Lastrellik/Calico-Home-Security/src/Properties.h

/*
  Properties.h - A class for Properties

  This class is intended to be included in any class which needs access to various Properties.
  For example, if your class needs to know whether the PI module is activte or not then
  you should include Properties.h in your class and call Properties::MODULE_PI to see
  whether it is configured to be true or not.
*/

#ifndef Properties_h
#define Properties_h

#include "Arduino.h"


class Properties {

  public:
    // ********** GENERAL ********** //
    static boolean DEBUGGING_ACTIVE;
    static boolean LASER_AIMING_MODE;
    static int BAUD_RATE;
    static int ALARM_TRIPPED_TO_TRIGGERED_MILLIS;


    // ********** MODULES ********** //
    static boolean MODULE_BASE;
    static boolean MODULE_MINI;
    static boolean MODULE_WIFI;
    static boolean MODULE_PI;
    static boolean MODULE_IR;
    static boolean MODULE_TOUCHSCREEN;
    static boolean MODULE_TURRET;


    // ********** WIFI MODULE PROPERTIES ********** //
    static int WIFI_RX_PIN;
    static int WIFI_TX_PIN;
    static String WIFI_SSID;
    static String WIFI_PASSWORD;
    static int WIFI_CONNECT_RETRY_COUNT;
    static String IFTTT_MAKER_KEY;
    static String IFTTT_MAKER_EVENT;
    static String IFTTT_MAKER_URI;


    // ********** TURRET MODULE PROPERTIES ********** //
    static int TURRET_SLAVE_NUMBER;
    static int TURRET_COMMAND;

  private:

};

#endif
